sconnair/1182.02-TDR/imgDev/allVersionSingleProfile/V2-V8.jpg

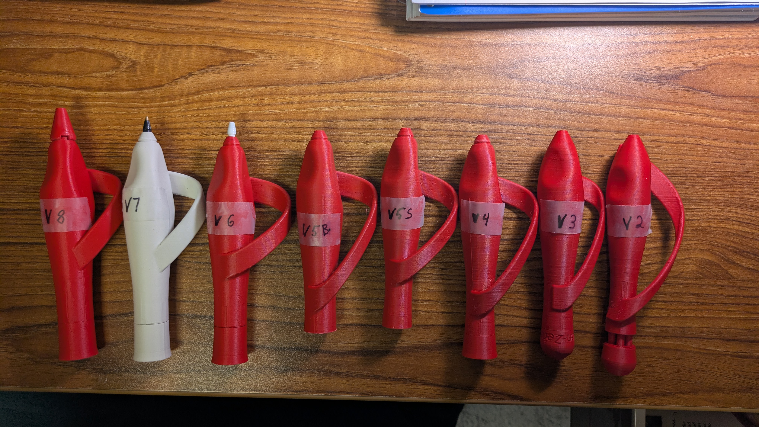
imgDev/allVersionSingleProfile/V2-V8.jpg
