sconnair/1182.02-TDR/imgDev/brainstormSketches/Daniel's sketches.jpg

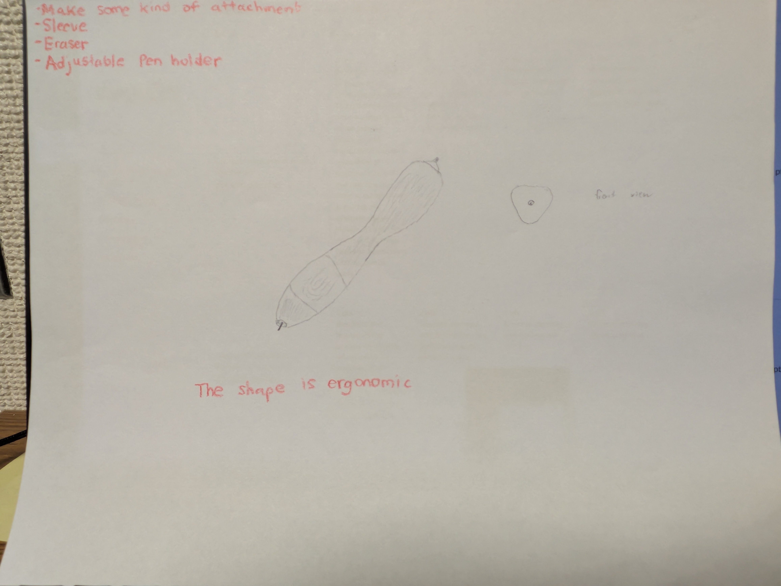
imgDev/brainstormSketches/Daniel's sketches.jpg
