sconnair/1182.02-TDR/imgDev/brainstormSketches/Design Development Photos/Mockup Photos/V2 Clay Mockup/Clay Mockup V2.jpg

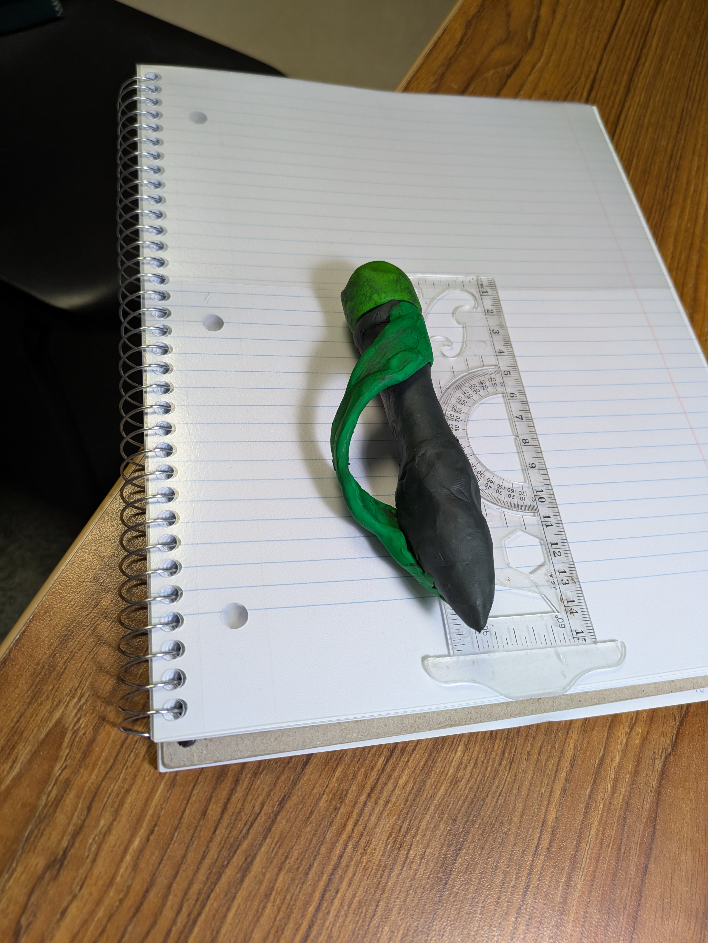
imgDev/brainstormSketches/Design Development Photos/Mockup Photos/V2 Clay Mockup/Clay Mockup V2.jpg
