sconnair/1182.02-TDR/imgDev/brainstormSketches/Design Development Photos/Mockup Photos/V2 Clay Mockup/v2b.jpg

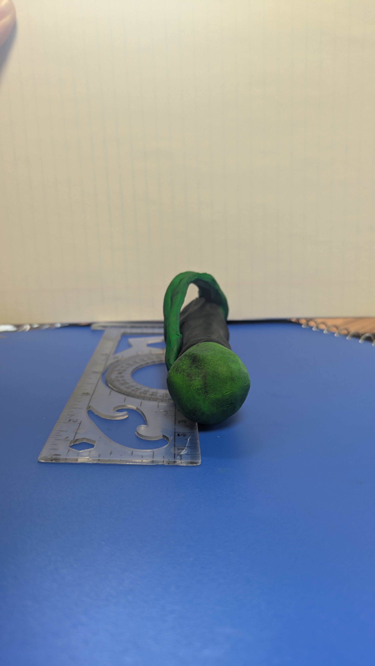
imgDev/brainstormSketches/Design Development Photos/Mockup Photos/V2 Clay Mockup/v2b.jpg
