sconnair/1182.02-TDR/imgDev/brainstormSketches/Design Development Photos/ZenPen V3 Print/PXL_20250328_203717379.jpg

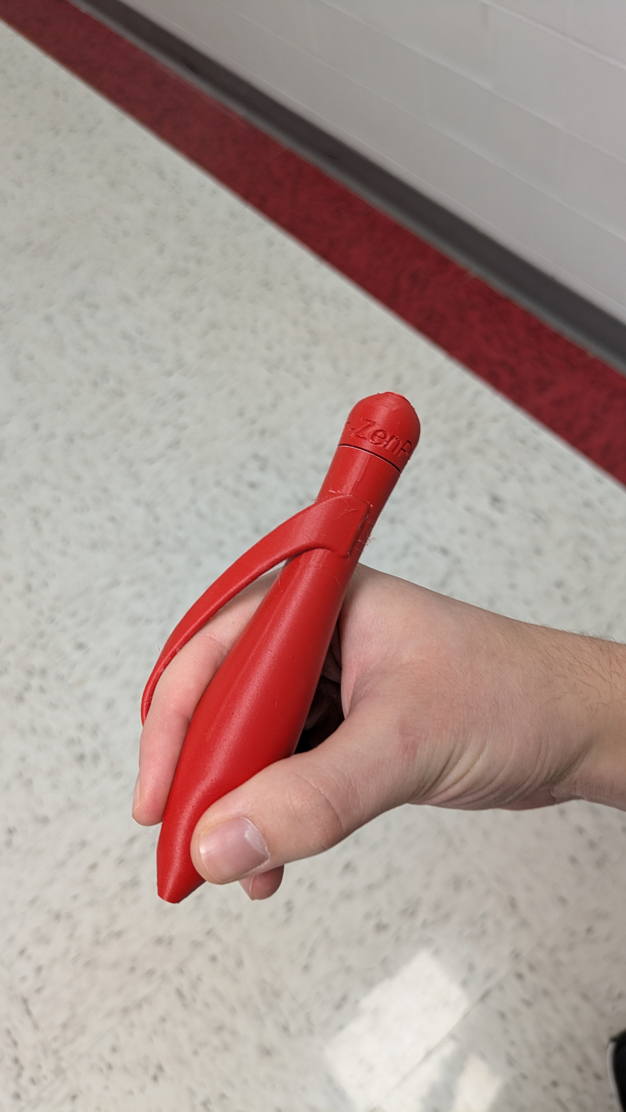
imgDev/brainstormSketches/Design Development Photos/ZenPen V3 Print/PXL_20250328_203717379.jpg
