sconnair/1182.02-TDR/imgDev/v2Print/PXL_20250328_164802392.jpg

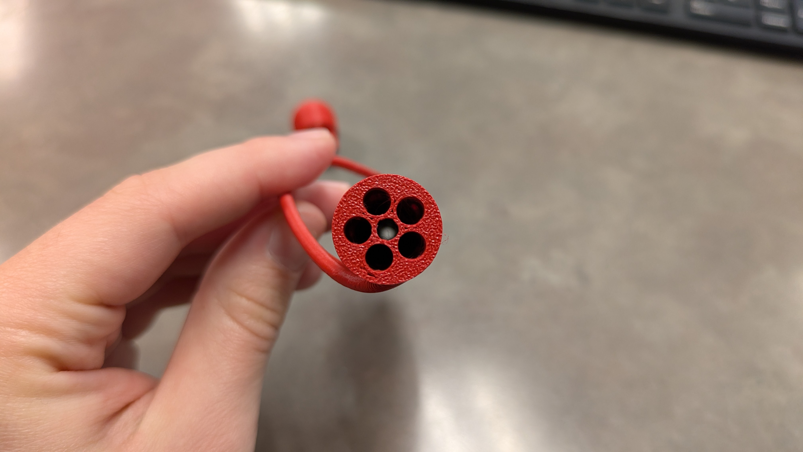
imgDev/v2Print/PXL_20250328_164802392.jpg
