sconnair/1182.02-TDR/imgDev/v2Print/PXL_20250328_164812540.jpg

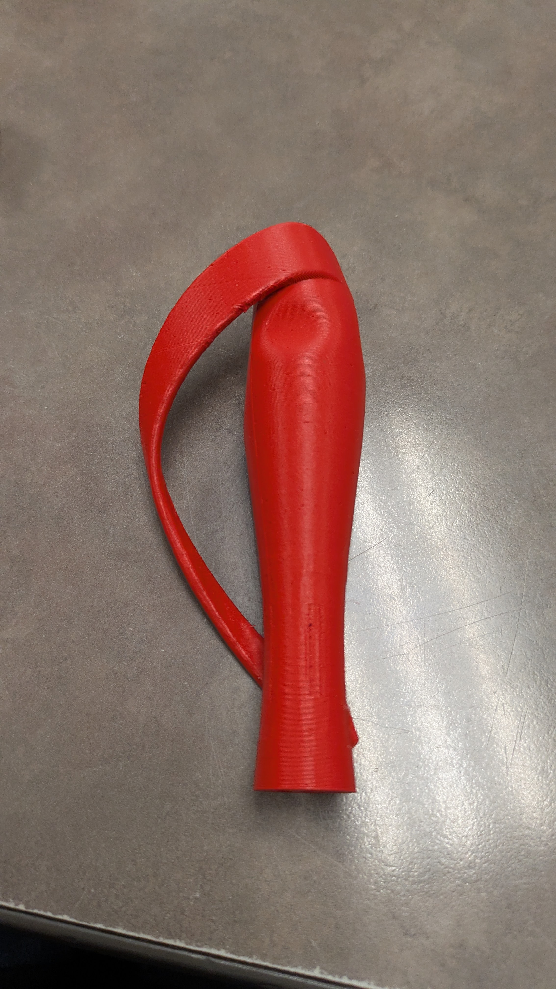
imgDev/v2Print/PXL_20250328_164812540.jpg
